rbckman/gonzopi_build/3d/gonzopi-hdmi-flexcap.png

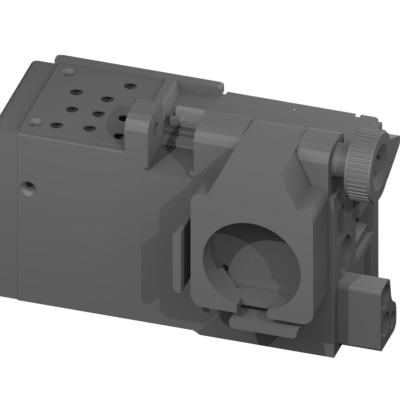
3d/gonzopi-hdmi-flexcap.png
