rbckman/gonzopi_build/3d/gonzopi-left-side-cap.png

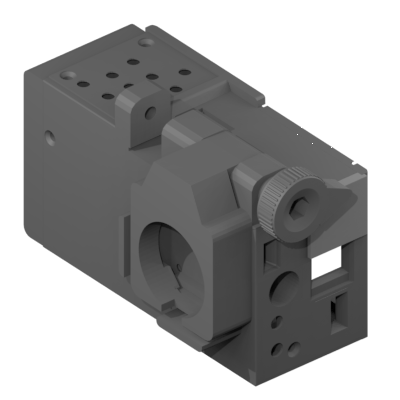
3d/gonzopi-left-side-cap.png
