rbckman/gonzopi_build/3d/gonzopi-picamera-clipgrip.png

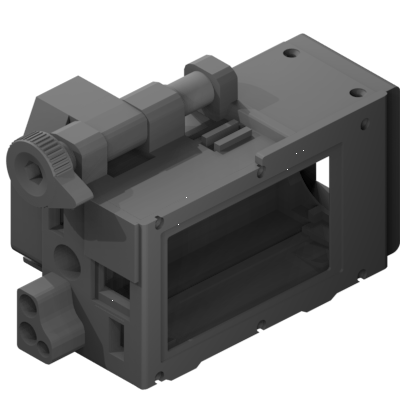
3d/gonzopi-picamera-clipgrip.png
