rbckman/gonzopi_build/3d/gonzopi-picamera-hq-body-lid.png

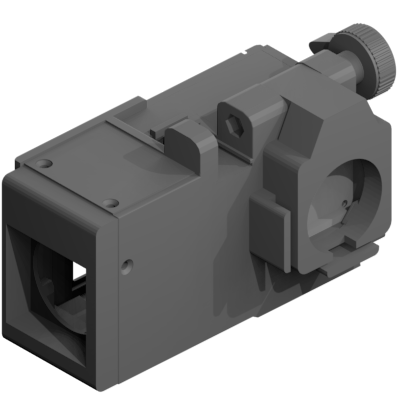
3d/gonzopi-picamera-hq-body-lid.png
