rbckman/gonzopi_build/3d/gonzopi-screen-lid-hyperpixel-touch.png

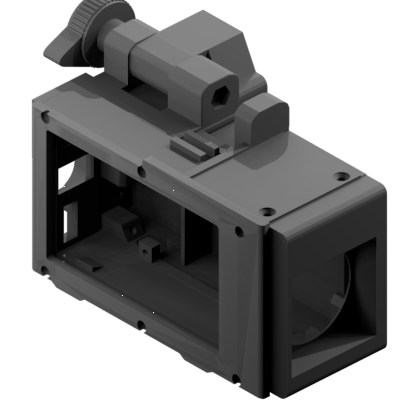
3d/gonzopi-screen-lid-hyperpixel-touch.png
