rbckman/gonzopi_build/3d/gonzopi-viewfinder-eyepiece.png

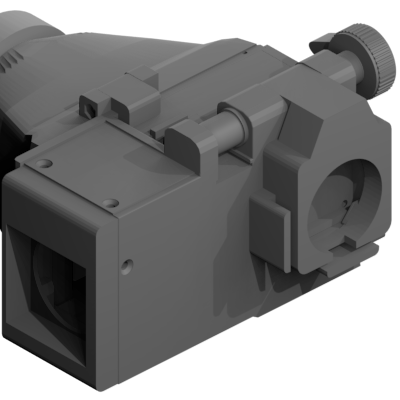
3d/gonzopi-viewfinder-eyepiece.png
