rbckman/gonzopi_build/3d/gonzopi-viewfinder-hyperpixel.png

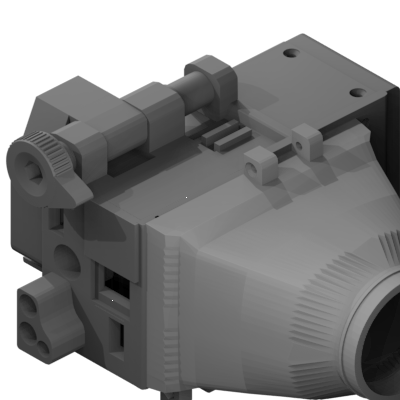
3d/gonzopi-viewfinder-hyperpixel.png
