rbckman/gonzopi_build/decals/gonzopi-buttons-black-white-flip.png

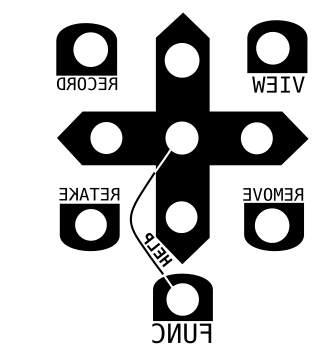
decals/gonzopi-buttons-black-white-flip.png
