rbckman/gonzopi_build/decals/gonzopi-buttons-bw.png

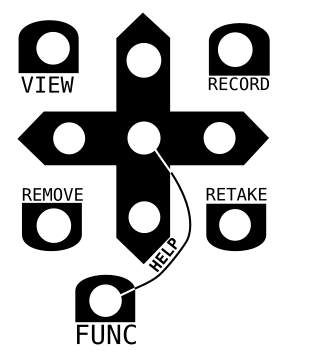
decals/gonzopi-buttons-bw.png
