rbckman/gonzopi_build/decals/gonzopi-buttons-func-button-pressed.png

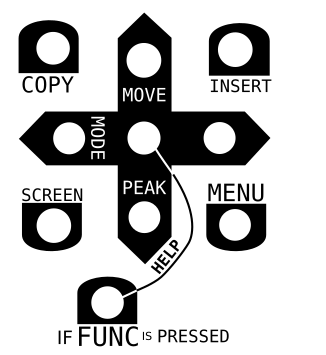
decals/gonzopi-buttons-func-button-pressed.png
