rbckman/gonzopi_build/decals/gonzopi-view-buttons.png

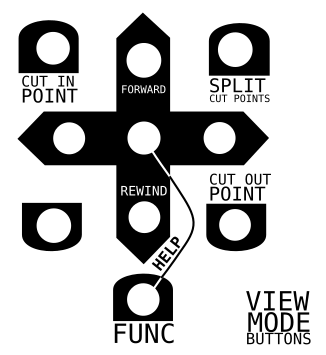
decals/gonzopi-view-buttons.png
