rbckman/gonzopi_build/3d/miniplug-bend-stopper.stl

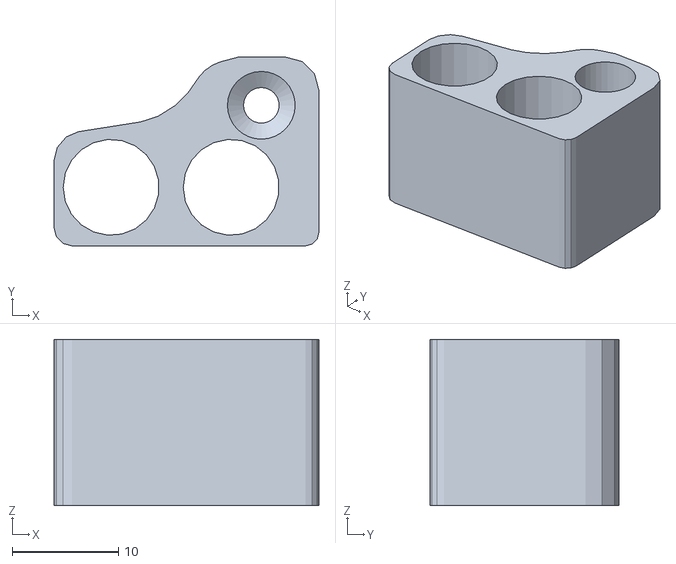
[picture p32: CAD file, 2025-05-05]
3d/miniplug-bend-stopper.stl
24.9 x 17.8 x 15.6
