rbckman/gonzopi_build/3d/gonzopi-mic-body.stl

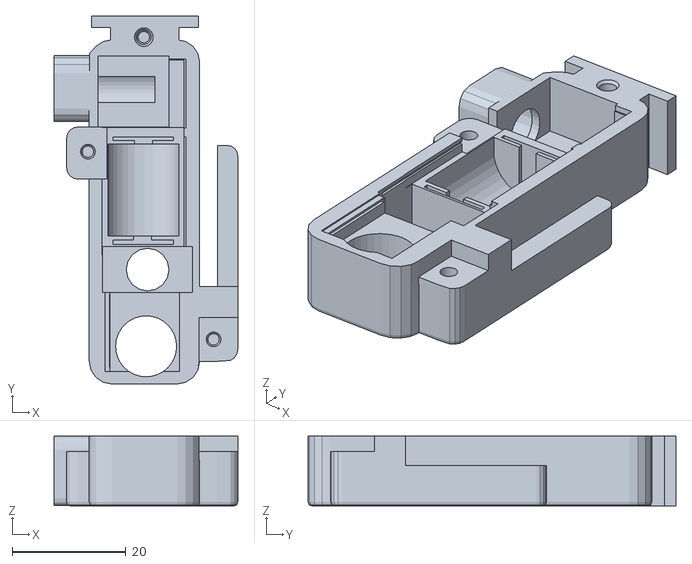
[picture p33: CAD file, 2025-05-05]
3d/gonzopi-mic-body.stl
32.3 x 64.8 x 12.3
