rbckman/gonzopi_build/3d/gonzopi-right-side.stl

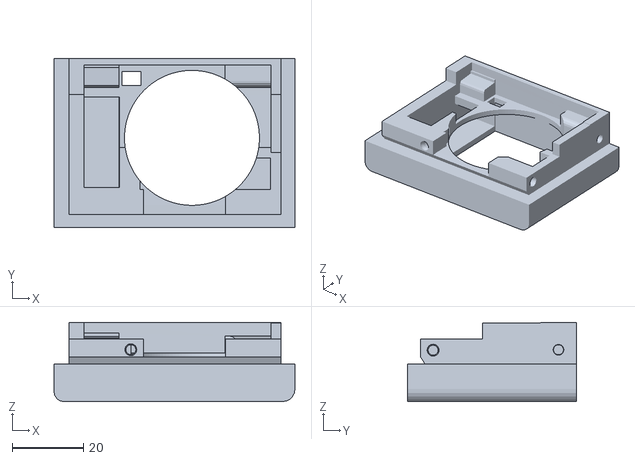
[picture p34: CAD file, 2025-05-05]
3d/gonzopi-right-side.stl
67.9 x 47.6 x 22.3
