rbckman/gonzopi_build/3d/gonzopi-screen-lid-ugeek.stl

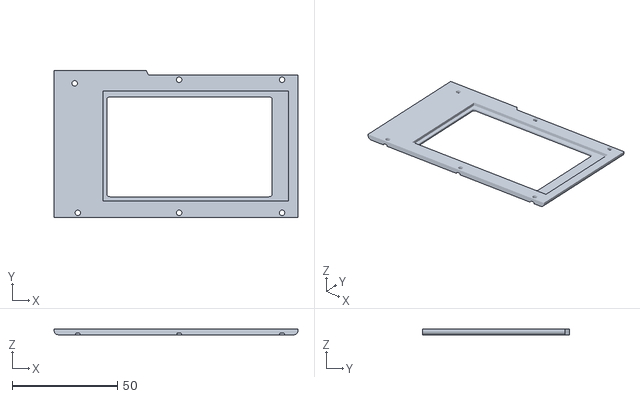
[picture p35: CAD file, 2025-05-05]
3d/gonzopi-screen-lid-ugeek.stl
115.7 x 69.6 x 2.70
