rbckman/gonzopi_build/3d/gonzopi-viewfinder-hyperpixel.stl

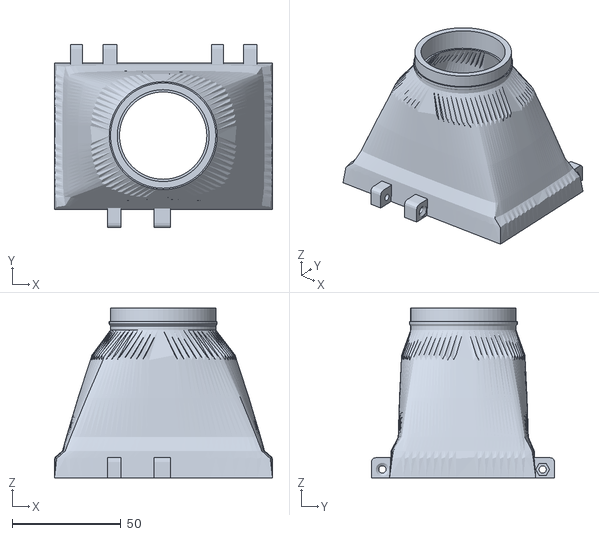
[picture p36: CAD file, 2025-05-05]
3d/gonzopi-viewfinder-hyperpixel.stl
100.2 x 84.3 x 78.0
