rbckman/gonzopi_build/3d/gonzopi-picamera-clipgrip.stl

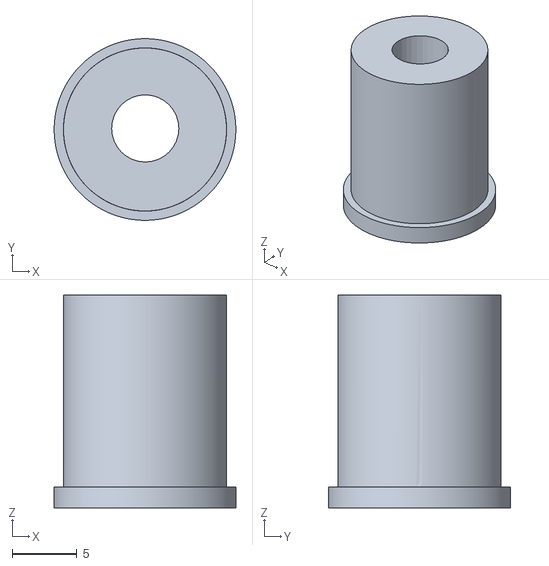
[picture p37: CAD file, 2025-05-05]
3d/gonzopi-picamera-clipgrip.stl
14.1 x 14.1 x 16.5
