rbckman/gonzopi_build/3d/gonzopi-button-plate-bottom.stl

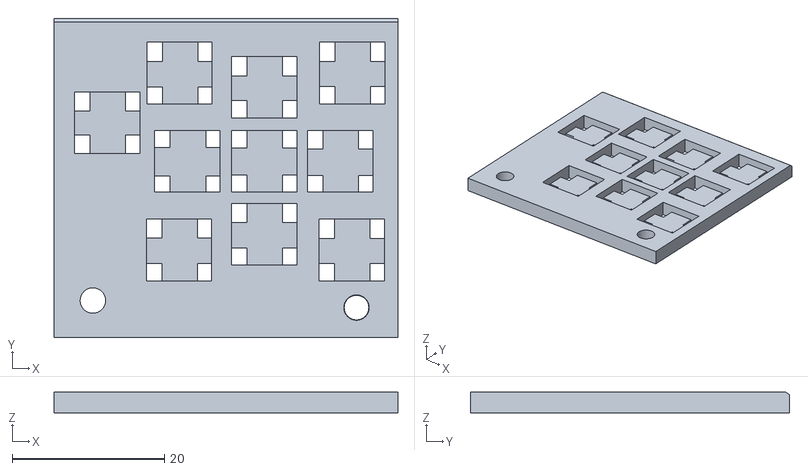
[picture p38: CAD file, 2025-05-05]
3d/gonzopi-button-plate-bottom.stl
45.1 x 41.9 x 2.71
