rbckman/gonzopi_build/3d/gonzopi-left-side-pi4.stl

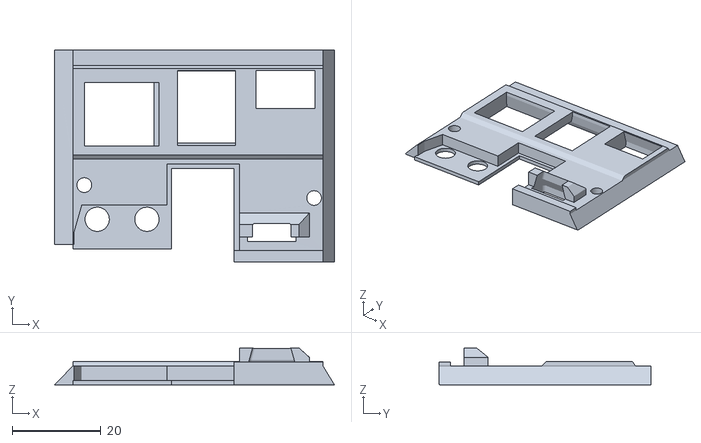
[picture p39: CAD file, 2025-05-05]
3d/gonzopi-left-side-pi4.stl
63.2 x 47.9 x 8.32
