rbckman/gonzopi_build/3d/gonzopi-body.stl

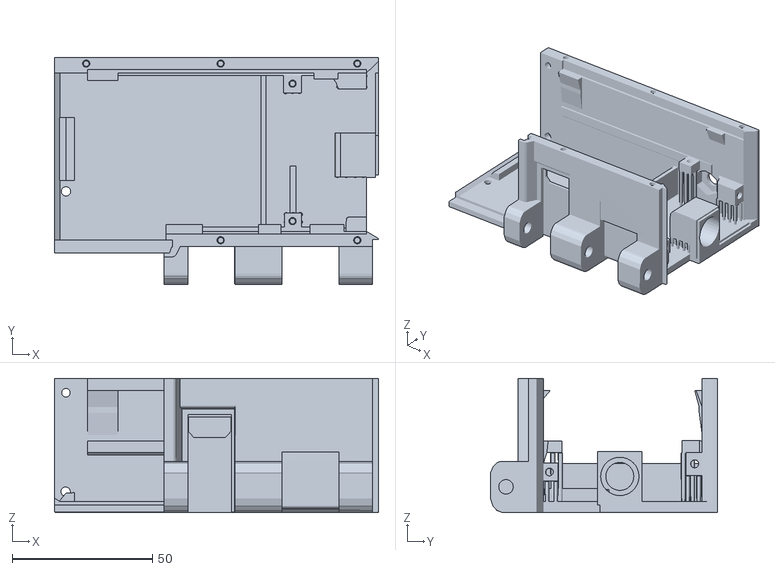
[picture p40: CAD file, 2025-05-05]
3d/gonzopi-body.stl
115.7 x 81.2 x 47.9
