rbckman/gonzopi_build/3d/viewfinder-clip-bridge.stl

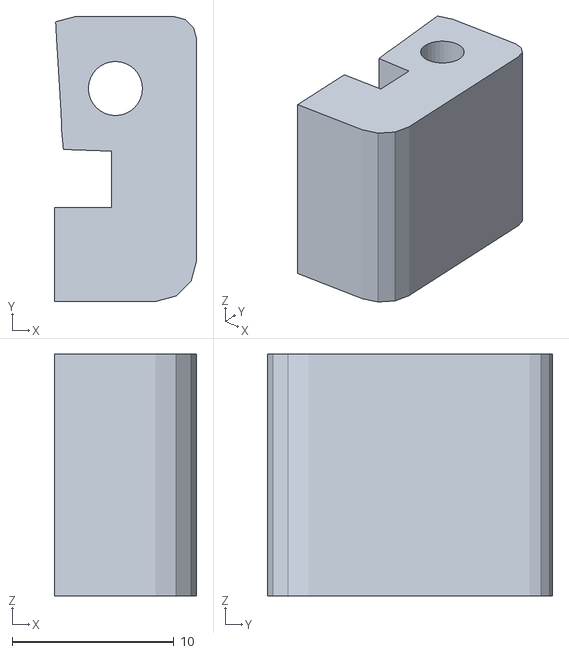
[picture p41: CAD file, 2025-05-05]
3d/viewfinder-clip-bridge.stl
8.80 x 17.6 x 14.9
