rbckman/gonzopi_build/3d/gonzopi-body-pi4.stl

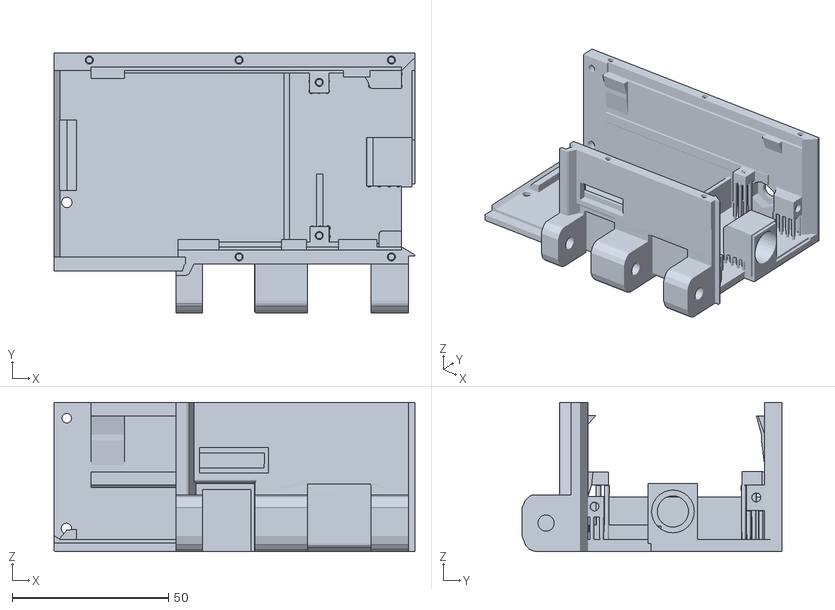
[picture p42: CAD file, 2025-05-05]
3d/gonzopi-body-pi4.stl
115.7 x 83.3 x 47.9
