rbckman/gonzopi_build/3d/viewfinder_extension.stl

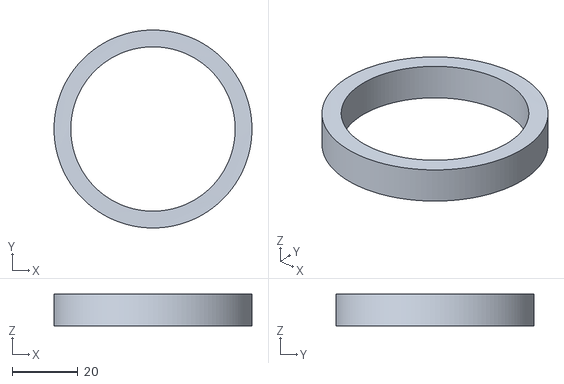
[picture p43: CAD file, 2023-11-22]
3d/viewfinder_extension.stl
60.3 x 60.3 x 9.68
