rbckman/gonzopi_build/3d/button-symbols.stl

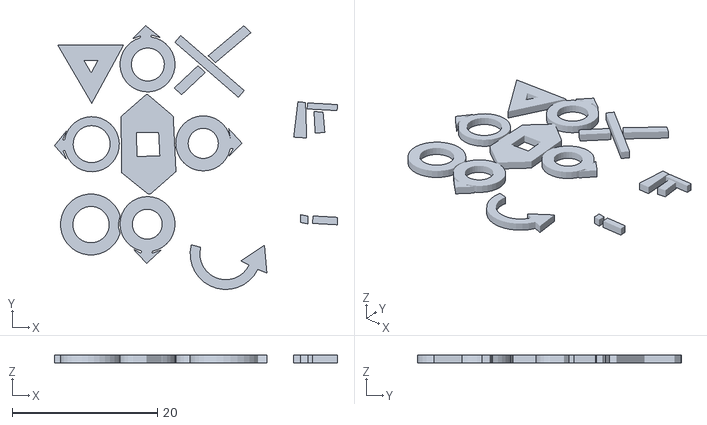
[picture p44: CAD file, 2023-11-22]
3d/button-symbols.stl
39.0 x 36.4 x 1.10
