rbckman/gonzopi_build/3d/tarinaloop.stl

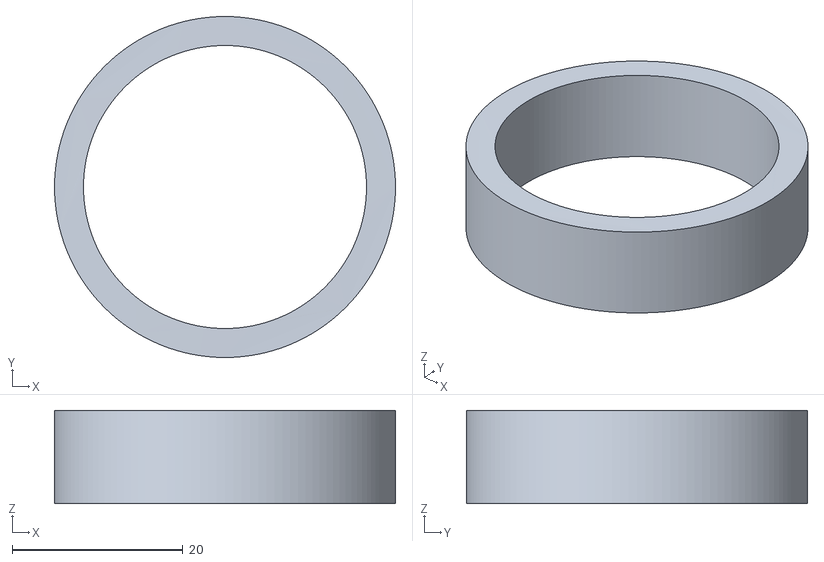
[picture p45: CAD file, 2023-11-22]
3d/tarinaloop.stl
40.0 x 40.0 x 11.0
